SnoWHandS/screaming-solar-cicada/resources/08_04_2026/oscillator.asc

C1: Cap; 1n
C2: Cap; 1n
M1: nmos; NDC7002N
Q1: npn; BC847B
Q2: npn; BC847B
R1: Res; 1k
R2: Res; 170k
R3: Res; 170k
R4: Res; 1k
R5: Res; 50
V1: Voltage; 3
Named nets: 0
.tran 0 1 0.001
